faironnerie-abc/arduiciole/assets/fds2015.png

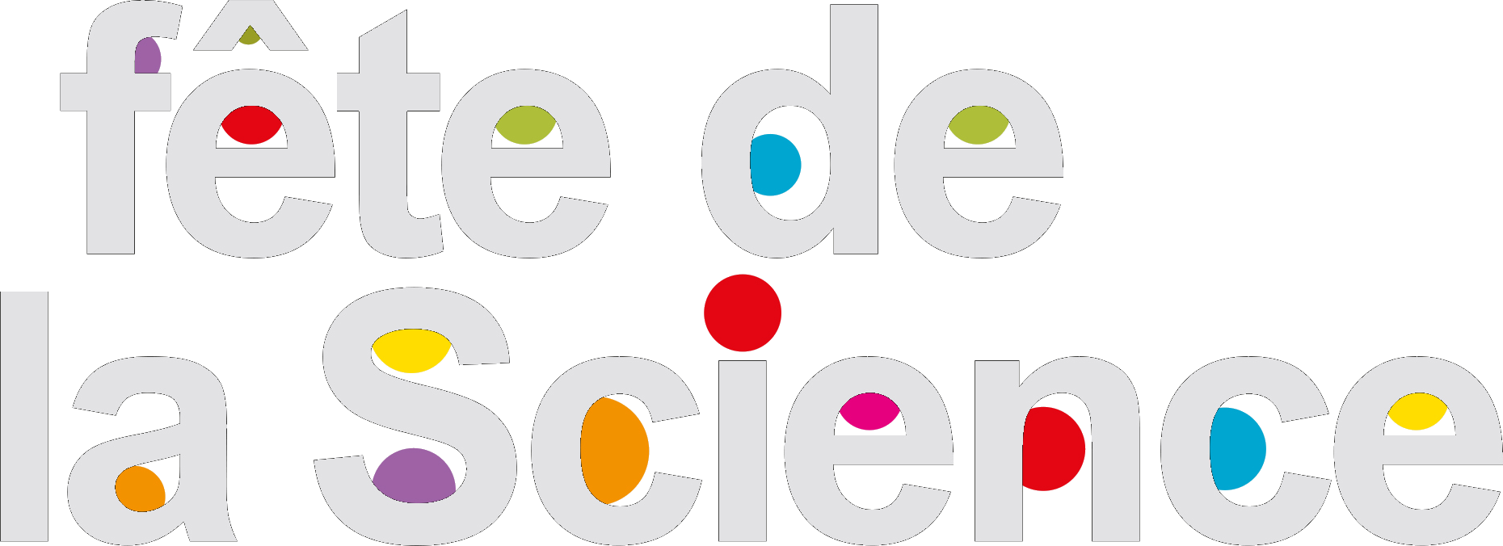
assets/fds2015.png
