faironnerie-abc/arduiciole/assets/grass.png

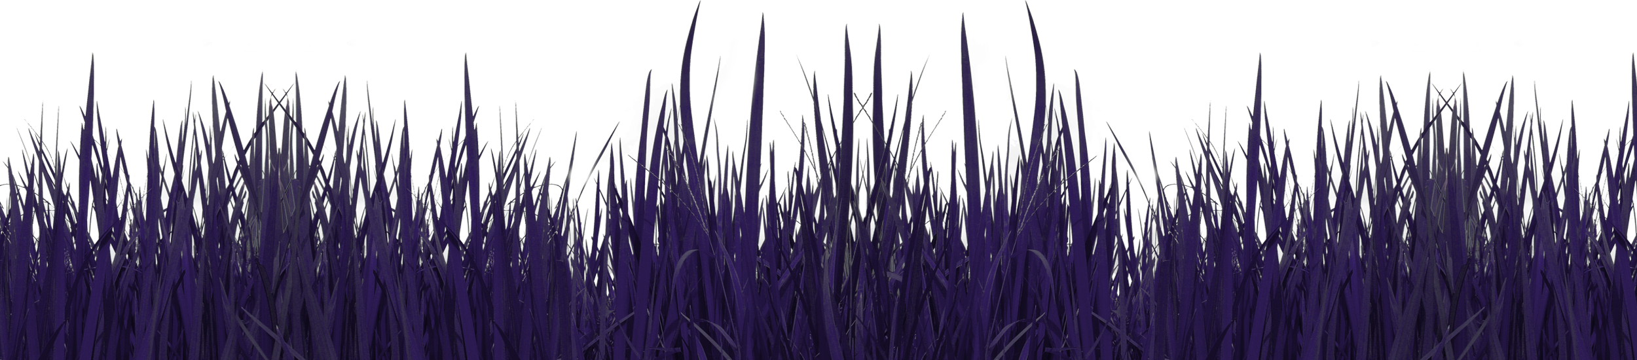
assets/grass.png
