faironnerie-abc/arduiciole/assets/tree.png

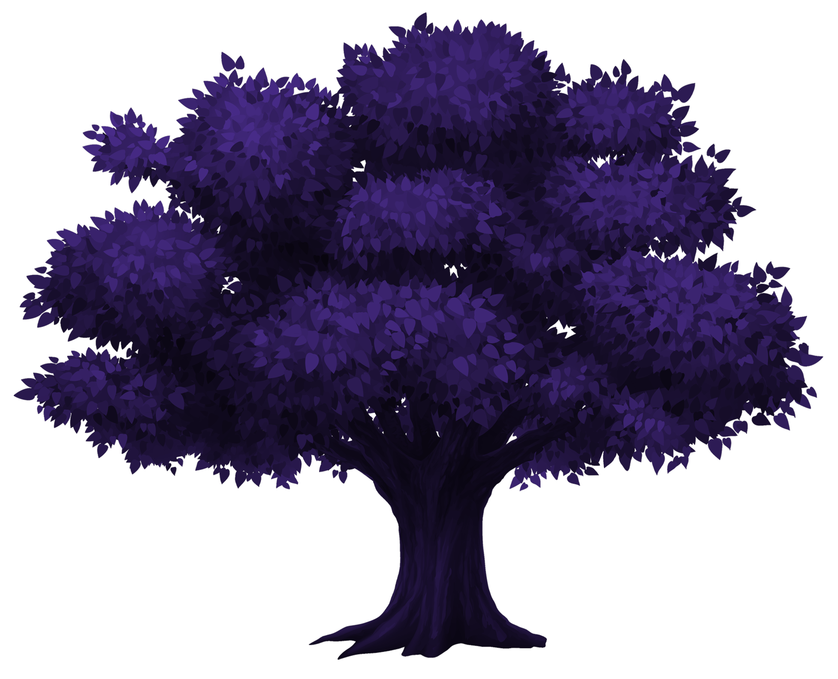
assets/tree.png
