faironnerie-abc/arduiciole/poster/centre/centre.png

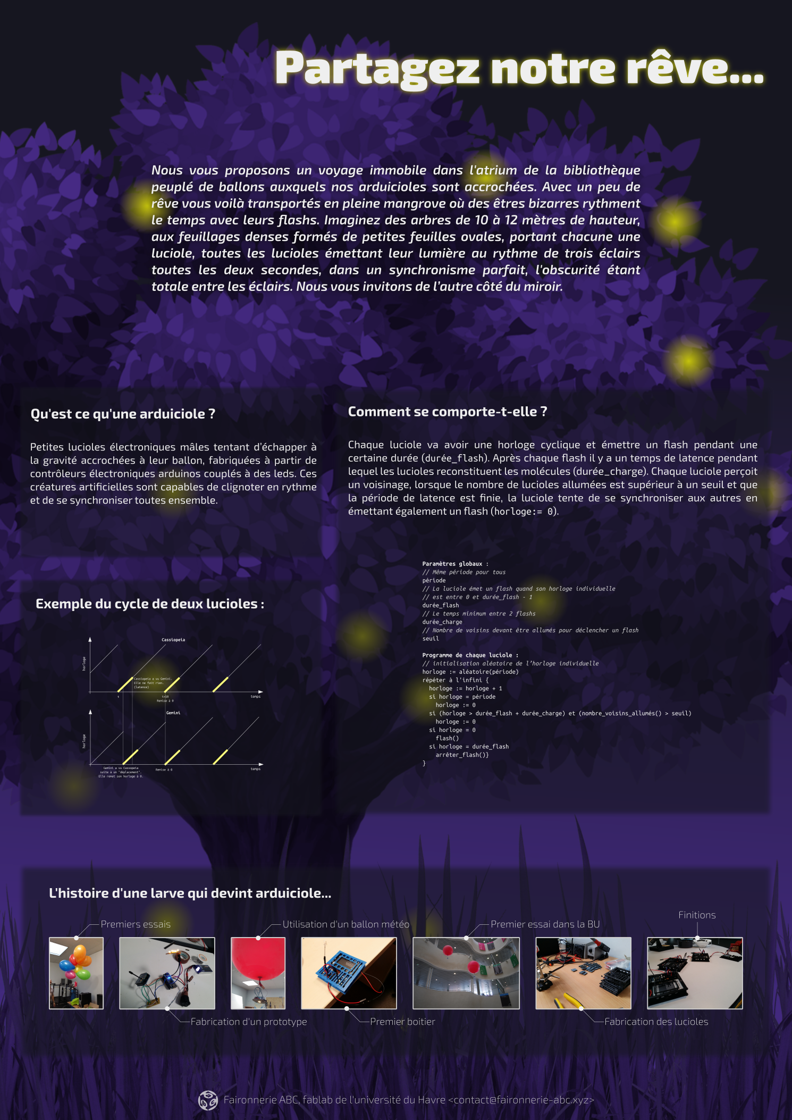
poster/centre/centre.png
