faironnerie-abc/arduiciole/poster/figures/brain.png

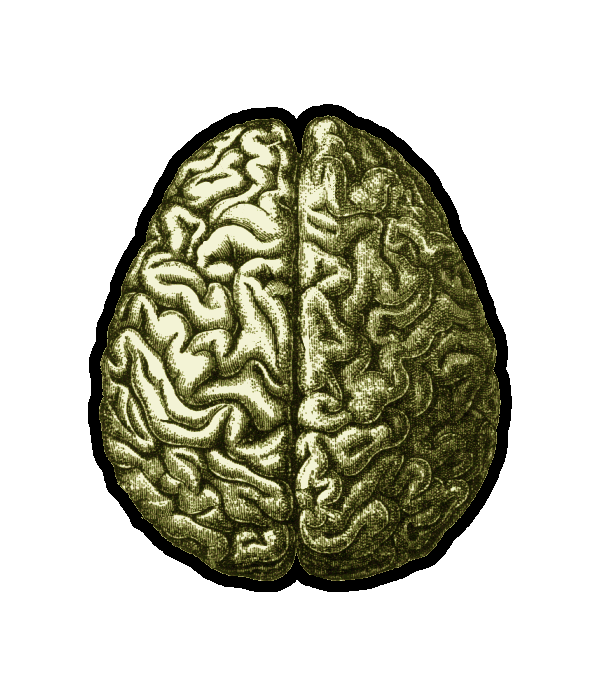
poster/figures/brain.png
