faironnerie-abc/arduiciole/poster/figures/cricket.jpg

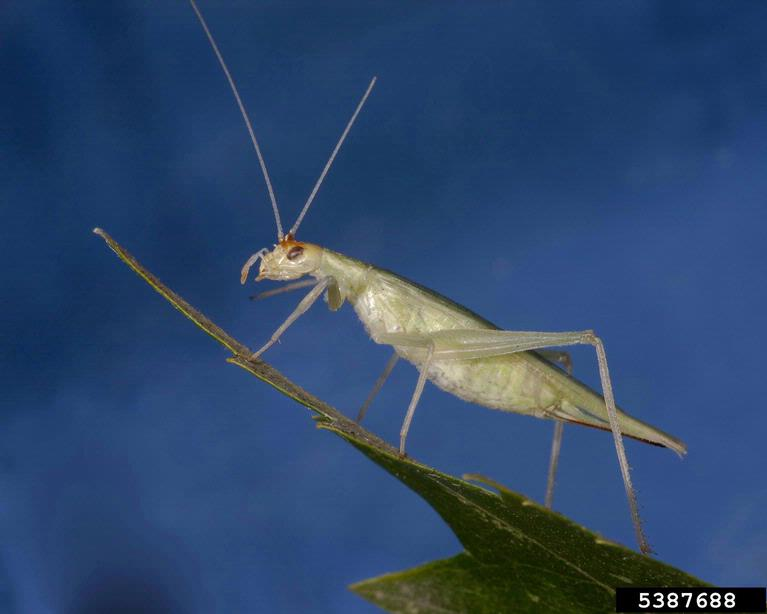
poster/figures/cricket.jpg
