faironnerie-abc/arduiciole/poster/figures/firefly-closeup.png

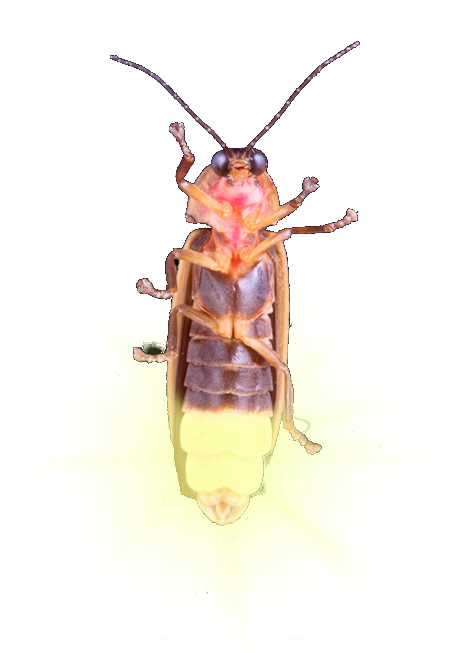
poster/figures/firefly-closeup.png
