faironnerie-abc/arduiciole/poster/figures/horloge-biologique.jpg

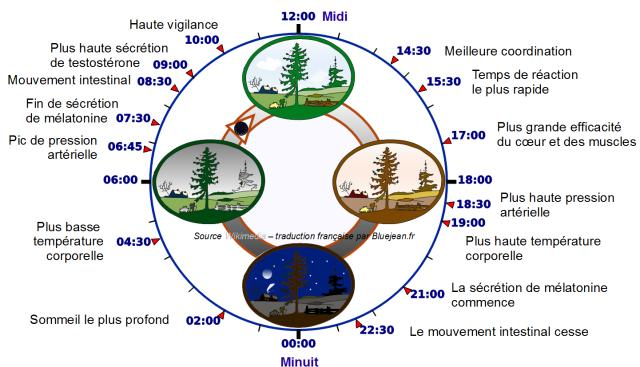
poster/figures/horloge-biologique.jpg
