faironnerie-abc/arduiciole/poster/figures/horloge_huygens.png

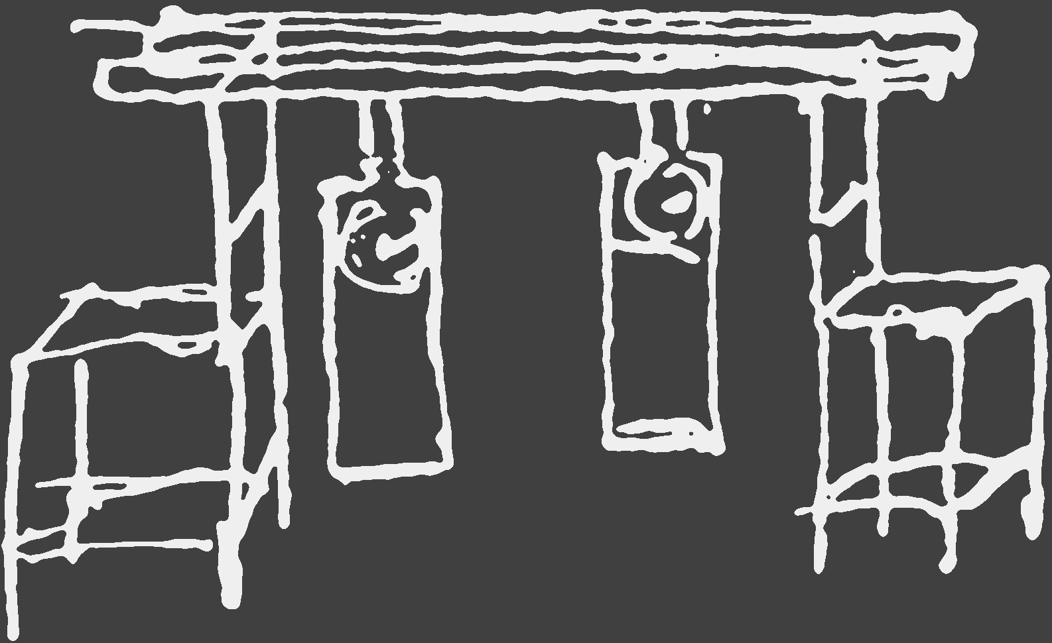
poster/figures/horloge_huygens.png
