faironnerie-abc/arduiciole/poster/figures/TL_01.jpg

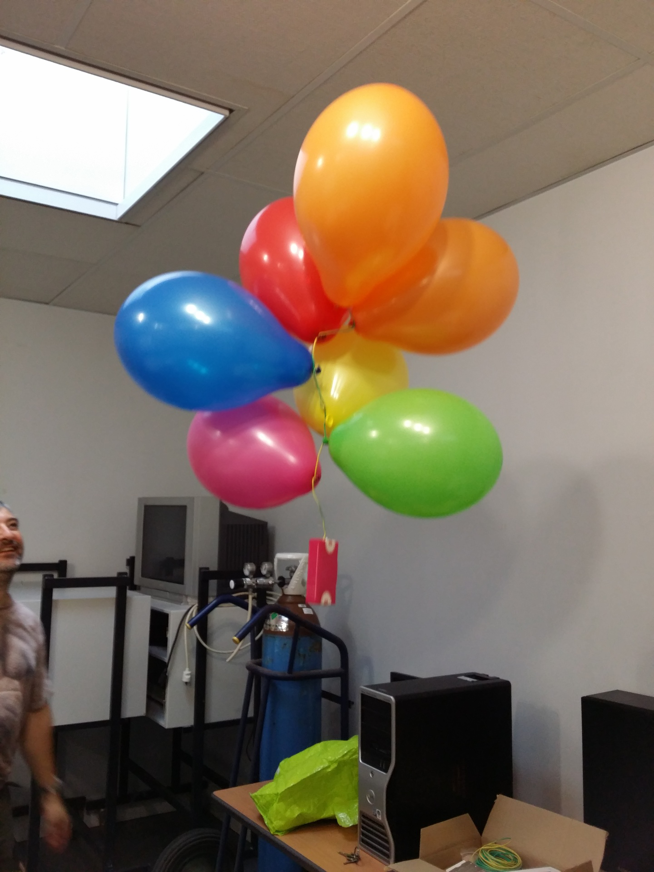
poster/figures/TL_01.jpg
