faironnerie-abc/arduiciole/poster/figures/TL_02.jpg

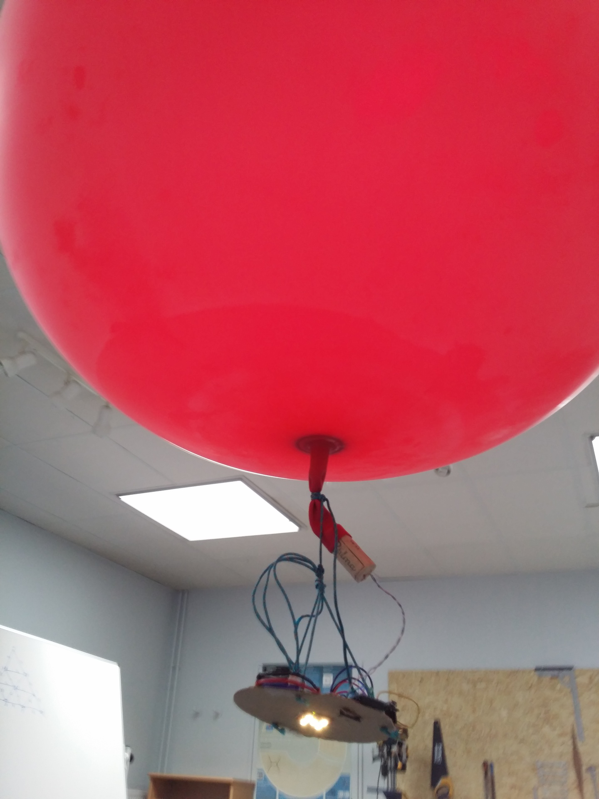
poster/figures/TL_02.jpg
