faironnerie-abc/arduiciole/poster/figures/TL_03.jpg

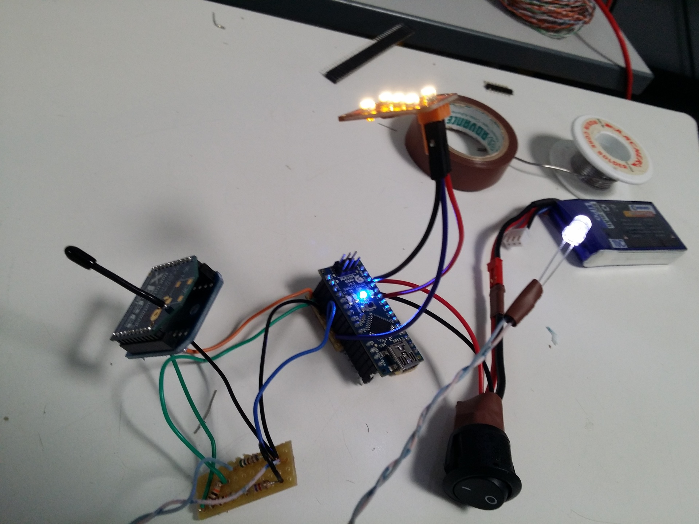
poster/figures/TL_03.jpg
