faironnerie-abc/arduiciole/poster/figures/TL_06.jpg

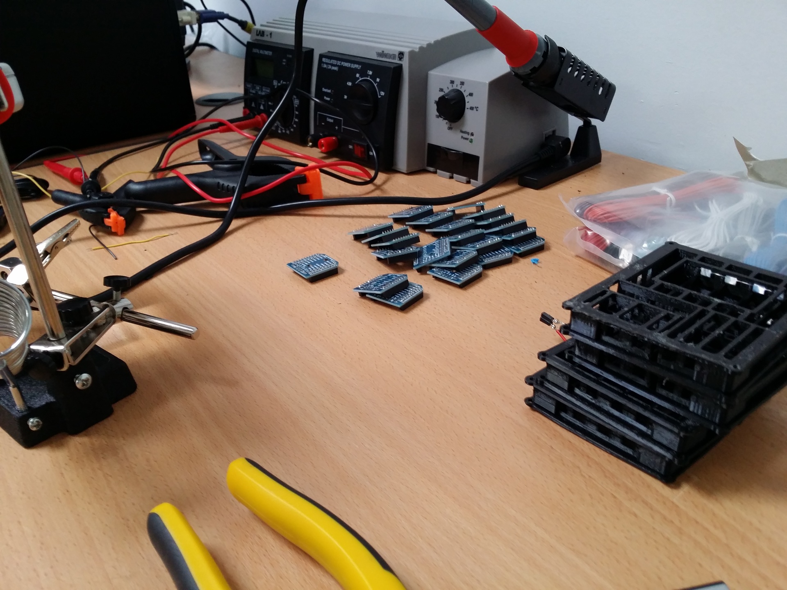
poster/figures/TL_06.jpg
