faironnerie-abc/arduiciole/poster/gauche/gauche.png

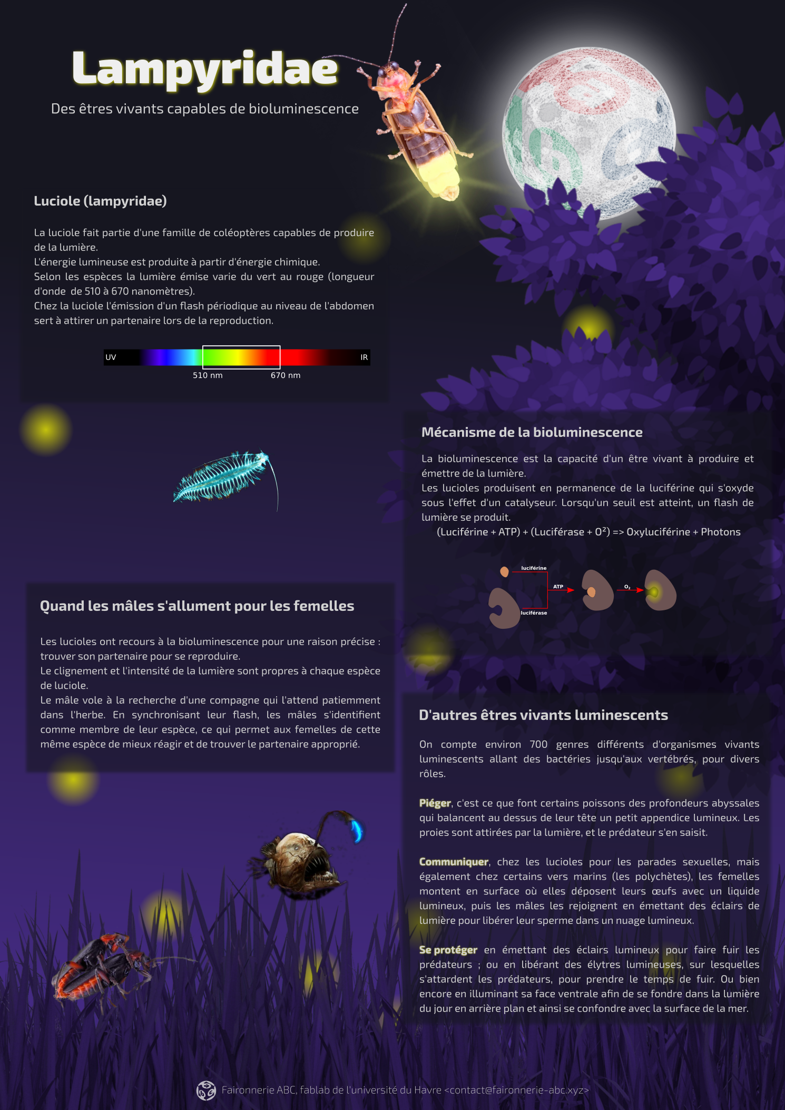
poster/gauche/gauche.png
