faironnerie-abc/arduiciole/poster/partenaires/partenaires.png

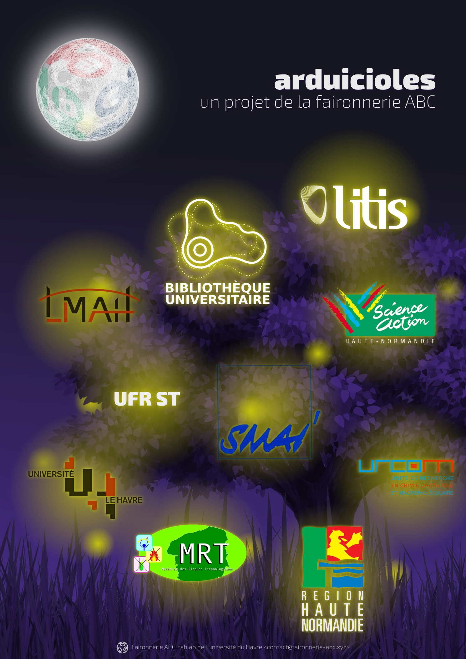
poster/partenaires/partenaires.png
