faironnerie-abc/arduiciole/poster/synchro/synchro-v2.png

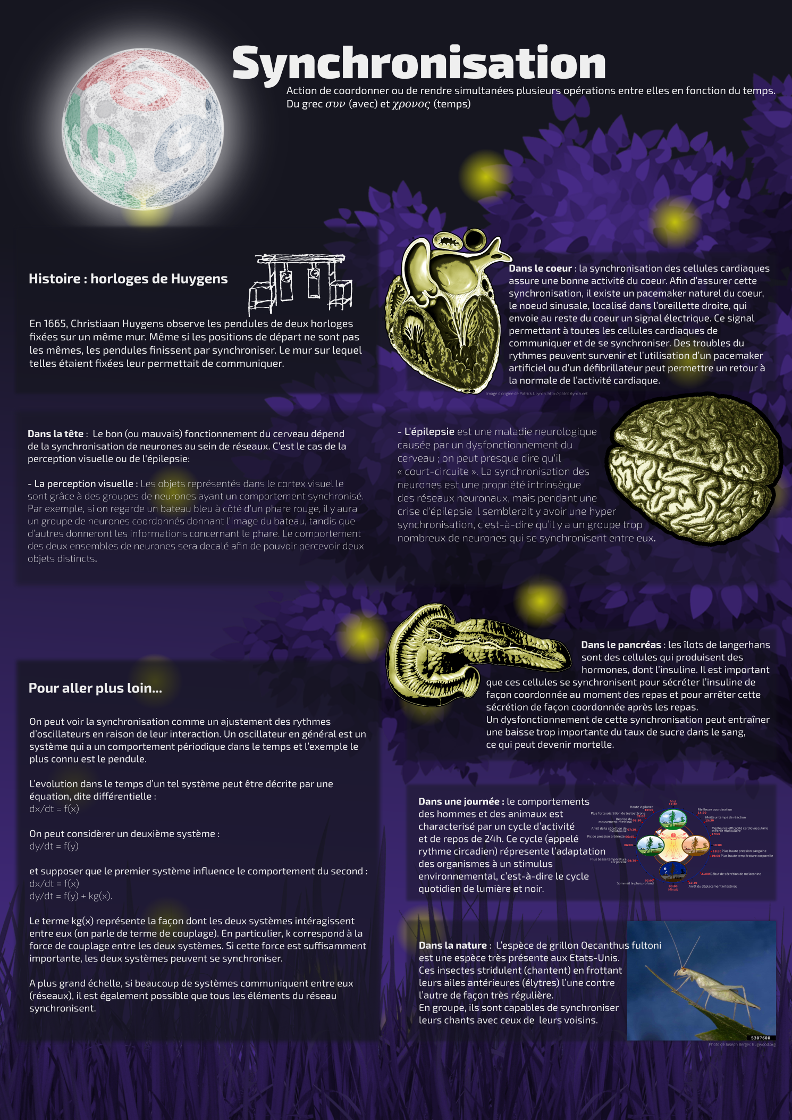
poster/synchro/synchro-v2.png
