faironnerie-abc/arduiciole/poster/synchro/synchro.png

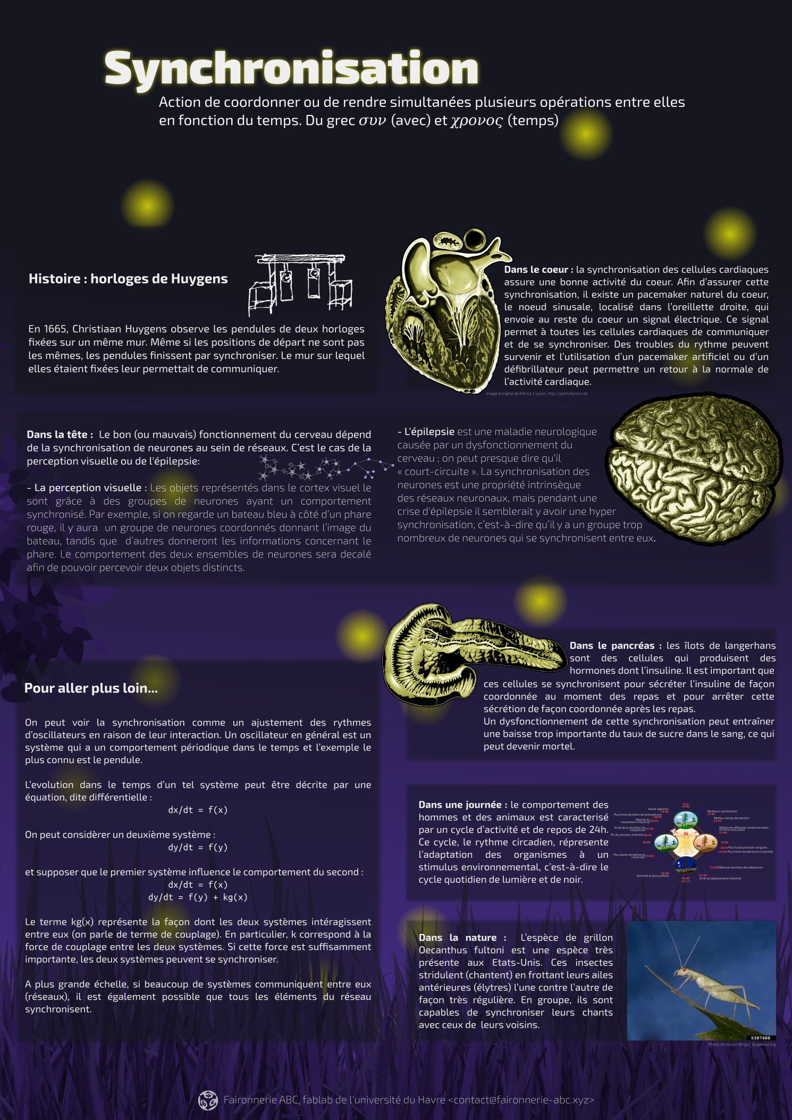
poster/synchro/synchro.png
