faironnerie-abc/arduiciole/poster/synchro/synchroDO.png

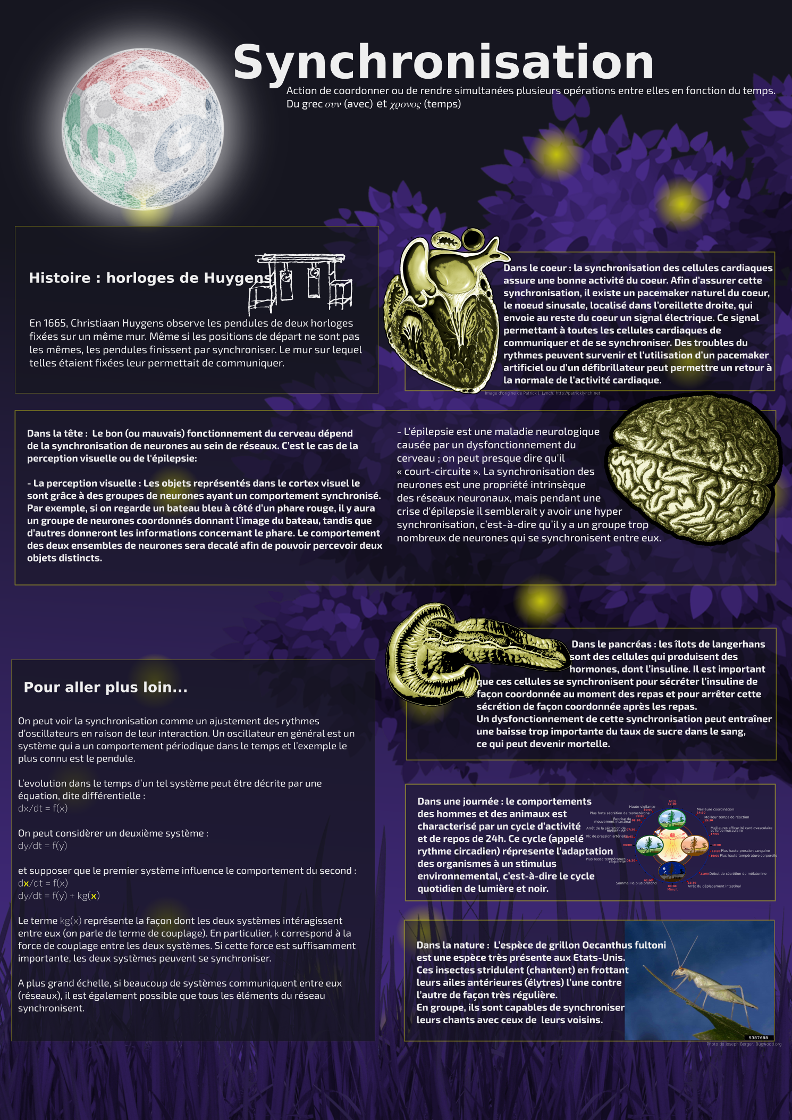
poster/synchro/synchroDO.png
