faironnerie-abc/arduiciole/screenshot.jpg

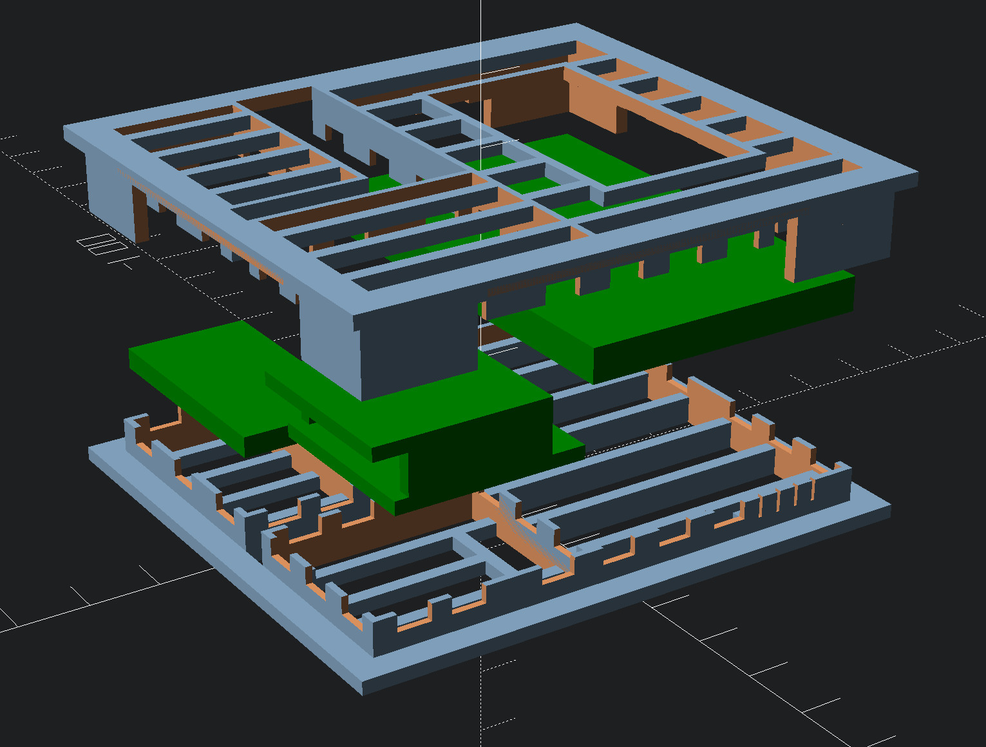
screenshot.jpg
